amaarayman-2006/smart-nursery-project/GUI/processing.py

import sounddevice as sd
import soundfile as sf
import noisereduce as nr
import webrtcvad as wvad
import os
import numpy as np
import pandas as pd
import librosa
import time

##############this code records short samples (each of 30 ms), and if noise is detected, 
# it records an audio file os length 3 min, removes back-noise, and saves it and its original copy locally
# note: that only occurs once. In other words, the whole script will need to be re-runned to check for a new 3-min recording ######################

def process_and_save_audio(output_filename="after noise removal.wav", duration=10, sr=16000,log_callback=None):

    """
    Captures mic input, removes background noise, runs VAD, 
    and saves the result to a WAV audio file on disk.
    """
    #print("\n--------------------------------------------------")
    if log_callback:
        log_callback("Starting audio recording process...")
    if log_callback:
        log_callback(f"Listening on microphone for {duration} seconds... Speak or play cry sound now!")
    
    # 1. Capture raw audio from laptop mic
    t0 = time.time()
    raw_audio = sd.rec(int(duration * sr), samplerate=sr, channels=1, dtype='float32')
    sd.wait()  # Hardware blocking pause for audio capture
    if log_callback:
        log_callback(f"Recording finished in {time.time() - t0:.2f}s. Audio captured into RAM.")

    # Flatten audio matrix to 1D vector
    raw_audio = np.squeeze(raw_audio)

    max_val = np.max(np.abs(raw_audio))
            
    # 2. Noise Floor Guard: Ignore frame if it's just room silence
    if max_val < 0.01:
        return False
        
    # 3. Controlled Peak Normalization (scales peak to 80% maximum, avoiding hard clipping)
    raw_audio = raw_audio / max_val * 0.8
    
    #print("Applying noise reduction filter...")
    t0 = time.time()
    clean_audio = nr.reduce_noise(
        y=raw_audio, 
        sr=sr, 
        prop_decrease=0.7, 
        stationary=True
    )
    if log_callback:
        log_callback(f"Noise removed successfully in {time.time() - t0:.2f}s.")
    
    # 3. Voice Activity Detection (VAD)
    if log_callback:
        log_callback("Running Voice Activity Detection (WebRTC VAD)...")
    t0 = time.time()
    
    vad = wvad.Vad(1)  # Change 0 to 3 in both functions
    pcm_data = (clean_audio * 32767).astype(np.int16).tobytes()
    frame_bytes = int(sr * 0.030 * 2)  # 30ms frame size
    total_frames = len(pcm_data) // frame_bytes
    
    voiced_frames = sum(
        vad.is_speech(pcm_data[i * frame_bytes : (i + 1) * frame_bytes], sr)
        for i in range(total_frames)
    )
    
    speech_ratio = voiced_frames / max(1, total_frames)
    is_cry_detected = speech_ratio > 0.15
    if log_callback:
          log_callback(f"VAD analysis finished in {time.time() - t0:.3f}s. Voiced frame ratio: {speech_ratio:.1%}")
    
    # 4. Save to Audio File (.wav)
    if log_callback:
        log_callback("Finalizing output...")
    #if is_cry_detected:
    #sf.write("original1.wav", raw_audio,sr)
    #sf.write("after noise removal1.wav", clean_audio, sr)
    #print(f"SUCCESS: Voice/Cry detected! Cleaned audio file saved to '{output_filename}'")
    #print("done")
    return clean_audio
    '''#else:
        if log_callback:
            log_callback("NOTICE: No voice/cry detected in sample. Skipping WAV file saving.")
        print("test failed")
        return None'''

def is_cry_detected(duration=0.03, sr=16000):
    t0 = time.time()
    vad = wvad.Vad(1)

    raw_audio = sd.rec(int(duration * sr), samplerate=sr, channels=1, dtype='float32')
    sd.wait()  # Hardware blocking pause for audio capture
    raw_audio = np.squeeze(raw_audio)
    max_val = np.max(np.abs(raw_audio))
            
    # 2. Noise Floor Guard: Ignore frame if it's just room silence
    if max_val < 0.01:
        return False
        
    # 3. Controlled Peak Normalization (scales peak to 80% maximum, avoiding hard clipping)
    raw_audio = raw_audio / max_val * 0.8
    pcm_bytes = (raw_audio * 32767).astype(np.int16).tobytes() 
    # Validate frame byte size (must be exactly 960 bytes for 30ms at 16kHz)
    if len(pcm_bytes) != int(sr * duration * 2):
        return False
    return vad.is_speech(pcm_bytes, sr)

'''def is_cry_detected(duration=0.03, sr=16000, threshold=0.03):
    raw_audio = sd.rec(int(duration * sr), samplerate=sr, channels=1, dtype='float32')
    sd.wait()
    raw_audio = np.squeeze(raw_audio)
    
    # Calculate the volume/energy of the sound
    rms = np.sqrt(np.mean(raw_audio**2))
    
    # If the sound is louder than the threshold, trigger the recording
    return rms > threshold'''

def go(timeout_seconds=100, short_sample_duration= 0.03, long_sample_duration=10, log_callback=None): # Added a timeout parameter (e.g., 60 seconds)
    start_time = time.time()
    check = True
    def log(message):
        if log_callback:
            log_callback(message)
    while not is_cry_detected(duration=short_sample_duration):
        # Check if the total elapsed time has exceeded our limit
        elapsed_time = time.time() - start_time 

        if elapsed_time > timeout_seconds :
            if log_callback:
                log_callback(f"Timeout reached ({timeout_seconds}s) with no audio detected. Exiting loop.")
            return None # Return None so your pipeline knows no audio was recorded
        if check == True:
            print("No noise detected")
            check = False        
        if log_callback:
          log_callback("No noise detected")
    print("noise detected")
    if log_callback:
        log_callback("System initializing...")
    file = process_and_save_audio(duration=long_sample_duration)
    if log_callback:
       log_callback("Pipeline execution complete!")
    return file

#go()
